krisisurf/Hyperlapse-Robot/frontend/Hyperlapse_Robot_Mobile_Controller/app/src/main/java/com/kristian/dimitrov/hyperlapse_robot_mobile_controller/entity/RuleEntity.java

package com.kristian.dimitrov.hyperlapse_robot_mobile_controller.entity;

import com.kristian.dimitrov.hyperlapse_robot_mobile_controller.entity.stepper.CameraStepMotorEntity;
import com.kristian.dimitrov.hyperlapse_robot_mobile_controller.entity.stepper.MovementStepMotorEntity;

import java.io.Serializable;

public class RuleEntity implements Serializable, Cloneable {

    private final MovementStepMotorEntity leftMotor;
    private final MovementStepMotorEntity rightMotor;
    private final CameraStepMotorEntity panMotor;
    private final CameraStepMotorEntity tiltMotor;


    private TurnEntity turnEntity;

    public RuleEntity(MovementStepMotorEntity leftMotor, MovementStepMotorEntity rightMotor, CameraStepMotorEntity panMotor, CameraStepMotorEntity tiltMotor) {
        this.leftMotor = leftMotor;
        this.rightMotor = rightMotor;
        this.panMotor = panMotor;
        this.tiltMotor = tiltMotor;
    }

    public RuleEntity(TurnEntity turnEntity, CameraStepMotorEntity panMotor, CameraStepMotorEntity tiltMotor) {
        this.turnEntity = turnEntity;
        turnEntity.setRuleEntity(this);
        this.leftMotor = turnEntity.getLeftMotor();
        this.rightMotor = turnEntity.getRightMotor();

        this.panMotor = panMotor;
        this.tiltMotor = tiltMotor;
    }

    /**
     * Finds how much time will the rule take.
     *
     * @return max execution time in seconds
     */
    public double getExecutionTime() {
        double maxExecutionTimeMovement = Math.max(leftMotor.getExecutionTime(), rightMotor.getExecutionTime());
        double maxExecutionTimeCamera = Math.max(panMotor.getExecutionTime(), tiltMotor.getExecutionTime());

        return Math.max(maxExecutionTimeMovement, maxExecutionTimeCamera);
    }

    @Override
    public String toString() {
        return "{" +
                "leftMotor: " + leftMotor +
                ", rightMotor: " + rightMotor +
                ", panMotor: " + panMotor +
                ", tiltMotor: " + tiltMotor +
                '}';
    }

    public String superToString() {
        return super.toString();
    }

    public MovementStepMotorEntity getLeftMotor() {
        return leftMotor;
    }

    public MovementStepMotorEntity getRightMotor() {
        return rightMotor;
    }

    public CameraStepMotorEntity getPanMotor() {
        return panMotor;
    }

    public CameraStepMotorEntity getTiltMotor() {
        return tiltMotor;
    }

    @Override
    public RuleEntity clone() {
        try {
            RuleEntity clone = (RuleEntity) super.clone();
            // TODO: copy mutable state here, so the clone can't change the internals of the original
            return clone;
        } catch (CloneNotSupportedException e) {
            throw new AssertionError();
        }
    }

    public TurnEntity getTurnEntity() {
        return turnEntity;
    }

    public void setTurnEntity(TurnEntity turnEntity) {
        this.turnEntity = turnEntity;
        turnEntity.setRuleEntity(this);
    }
}
