krisisurf/Hyperlapse-Robot/frontend/Hyperlapse_Robot_Mobile_Controller/app/src/main/java/com/kristian/dimitrov/hyperlapse_robot_mobile_controller/fragments/TurningFragment.java

package com.kristian.dimitrov.hyperlapse_robot_mobile_controller.fragments;

import android.os.Bundle;
import android.view.LayoutInflater;
import android.view.View;
import android.view.ViewGroup;
import android.widget.Button;

import androidx.annotation.NonNull;
import androidx.annotation.Nullable;
import androidx.fragment.app.Fragment;

import com.kristian.dimitrov.hyperlapse_robot_mobile_controller.R;
import com.kristian.dimitrov.hyperlapse_robot_mobile_controller.activities.NumberInputPopupDialog;
import com.kristian.dimitrov.hyperlapse_robot_mobile_controller.entity.ArduinoRobot;
import com.kristian.dimitrov.hyperlapse_robot_mobile_controller.entity.RuleEntity;
import com.kristian.dimitrov.hyperlapse_robot_mobile_controller.entity.TurnEntity;
import com.kristian.dimitrov.hyperlapse_robot_mobile_controller.entity.stepper.StepMotorEntity;
import com.kristian.dimitrov.hyperlapse_robot_mobile_controller.exception.IncompatibleStepMotorArguments;


/**
 * A simple {@link Fragment} subclass.
 * create an instance of this fragment.
 */
public class TurningFragment extends Fragment {

    private static final String TAG = "TurningFragment";

    public static final String NUMBER_INPUT_POPUP_DIALOG_PARAM = "nipd";
    public static final String RULE_ENTITY_PARAM = "re";
    public static final String ARDUINO_ROBOT_PARAM = "ar";

    private NumberInputPopupDialog numberInputPopupDialog;
    private RuleEntity ruleEntity;
    private Button btnTurnAngle;
    private Button btnTurnRadius;
    private Button btnExecutionTime;

    private TurnEntity turnEntity;

    public TurningFragment() {
        // Required empty public constructor
    }

    /**
     * Use this factory method to create a new instance of
     * this fragment using the provided parameters.
     *
     * @return A new instance of fragment TurningFragment.
     */
    public static TurningFragment newInstance(NumberInputPopupDialog numberInputPopupDialog, RuleEntity ruleEntity, ArduinoRobot arduinoRobot) {
        TurningFragment fragment = new TurningFragment();

        Bundle args = new Bundle();
        args.putSerializable(NUMBER_INPUT_POPUP_DIALOG_PARAM, numberInputPopupDialog);
        args.putSerializable(RULE_ENTITY_PARAM, ruleEntity);
        args.putSerializable(ARDUINO_ROBOT_PARAM, arduinoRobot);

        fragment.setArguments(args);
        return fragment;
    }

    @Override
    public void onCreate(Bundle savedInstanceState) {
        super.onCreate(savedInstanceState);

        if (getArguments() != null) {
            numberInputPopupDialog = (NumberInputPopupDialog) getArguments().getSerializable(NUMBER_INPUT_POPUP_DIALOG_PARAM);
            ruleEntity = (RuleEntity) getArguments().getSerializable(RULE_ENTITY_PARAM);
            turnEntity = ruleEntity.getTurnEntity();
        }
    }

    @Override
    public View onCreateView(LayoutInflater inflater, ViewGroup container,
                             Bundle savedInstanceState) {
        // Inflate the layout for this fragment
        return inflater.inflate(R.layout.fragment_turning, container, false);
    }

    @Override
    public void onViewCreated(@NonNull View view, @Nullable Bundle savedInstanceState) {
        super.onViewCreated(view, savedInstanceState);

        btnTurnAngle = view.findViewById(R.id.btnTurnAngle);
        btnTurnAngle.setOnClickListener(this::buttonTurnAngleListener);

        btnTurnRadius = view.findViewById(R.id.btnTurnRadius);
        btnTurnRadius.setOnClickListener(this::buttonTurnRadiusListener);

        btnExecutionTime = requireView().findViewById(R.id.btnExecutionTime);
        btnExecutionTime.setText(getString(R.string.execution_time, (int) ruleEntity.getLeftMotor().getExecutionTime()));
        btnExecutionTime.setOnClickListener(this::buttonExecutionTimeListener);

        setupDefaultValues(view);
    }

    private void setupDefaultValues(View view) {
        btnTurnAngle.setText(view.getContext().getString(R.string.degree, turnEntity.getTurnAngle()));
        btnTurnRadius.setText(view.getContext().getString(R.string.centimeters, turnEntity.getTurnRadius()));
        btnExecutionTime.setText(getString(R.string.execution_time, turnEntity.getExecutionTime()));
    }

    private void buttonTurnRadiusListener(View view) {
        numberInputPopupDialog.setTitle(R.string.turn_radius);
        numberInputPopupDialog.setMinValue(0);
        numberInputPopupDialog.setMaxValue(Short.MAX_VALUE);
        numberInputPopupDialog.setValue(0);
        numberInputPopupDialog.setNegativeNumbers(true);
        numberInputPopupDialog.addNumberSelectedListener(turnRadius -> {
            turnEntity.setTurnRadius(turnRadius);
            btnTurnRadius.setText(view.getContext().getString(R.string.centimeters, turnRadius));
            btnExecutionTime.setText(view.getContext().getString(R.string.execution_time, turnEntity.getExecutionTime()));
        });
        numberInputPopupDialog.show();
    }

    private void buttonTurnAngleListener(View view) {
        numberInputPopupDialog.setTitle(R.string.turn_angle);
        numberInputPopupDialog.setMinValue(0);
        numberInputPopupDialog.setMaxValue(Short.MAX_VALUE);
        numberInputPopupDialog.setValue(0);
        numberInputPopupDialog.setNegativeNumbers(true);
        numberInputPopupDialog.addNumberSelectedListener(turnAngle -> {
            turnEntity.setTurnAngle(turnAngle);
            btnTurnAngle.setText(view.getContext().getString(R.string.degree, turnAngle));
            btnExecutionTime.setText(view.getContext().getString(R.string.execution_time, turnEntity.getExecutionTime()));
        });
        numberInputPopupDialog.show();
    }

    private void buttonExecutionTimeListener(View view) {
        StepMotorEntity longerPathMotor = (ruleEntity.getLeftMotor().getMeasurementValue() > ruleEntity.getRightMotor().getMeasurementValue()) ?
                ruleEntity.getLeftMotor() : ruleEntity.getRightMotor();
        int minExecTimeCelled = StepMotorEntity.getMinimalExecutionTimeCelled(longerPathMotor, (int) longerPathMotor.getMeasurementValue());

        numberInputPopupDialog.setTitle("Turning " + getString(R.string.label_execution_time));
        numberInputPopupDialog.setMinValue(minExecTimeCelled);
        numberInputPopupDialog.setMaxValue(Short.MAX_VALUE);
        numberInputPopupDialog.setValue(Math.max(minExecTimeCelled, Math.abs((int) longerPathMotor.getExecutionTime())));
        numberInputPopupDialog.setNegativeNumbers(false);
        numberInputPopupDialog.addNumberSelectedListener(executionTime -> {
            try {
                turnEntity.setExecutionTime(executionTime);
                btnExecutionTime.setText(getString(R.string.execution_time, executionTime));
            } catch (IncompatibleStepMotorArguments e) {
                e.printStackTrace();
            }
        });
        numberInputPopupDialog.show();
    }
}
